mookiedog/umod4-PCB/Spice/AdcDivider1.asc

C1: cap; 1nF
D2: schottky; RB541VM-40
R2: res; 20K
R3: res; 5K1
V1: voltage; PULSE(0 20 0 100ms 0 0 1)
V2: voltage; 3.3; Rser=1
Named nets: 0, VADC, Vbatt
.tran 0.1
