mookiedog/umod4-PCB/Spice/VoltageClamp.asc

D1: zener; CDZV15B
D2: zener; CDZV15B
Q1: npn; 2SCR375P
R1: res; 1000R
R2: res; R=if(abs(v(VOUT)), 10, (V(VOUT)**2)/0.4)
V1: voltage; PULSE(12 60 0.1 0.1 0.2 0 1)
Named nets: 0, VOUT, VB, Vin
.tran .5
